walked22/Stacy/climate2/both.png

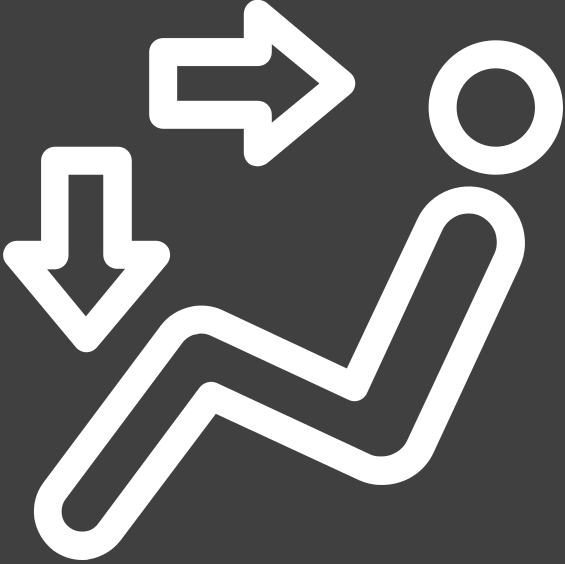
climate2/both.png
