walked22/Stacy/climate2/cold.png

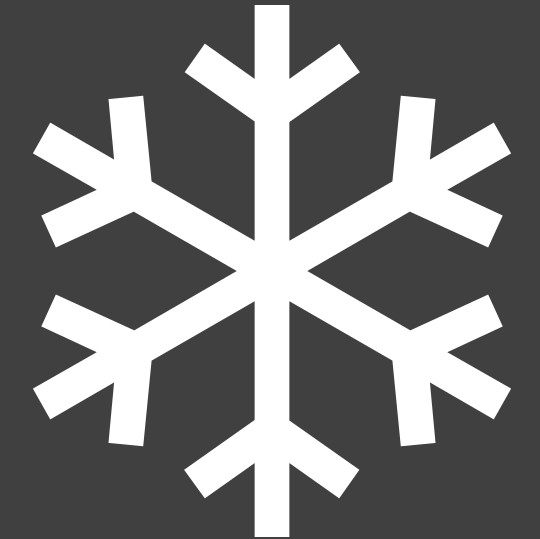
climate2/cold.png
