walked22/Stacy/climate2/defrost.png

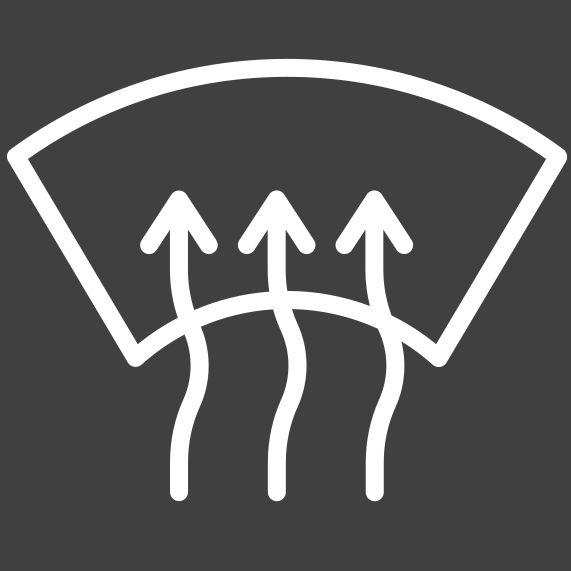
climate2/defrost.png
