walked22/Stacy/climate2/face.png

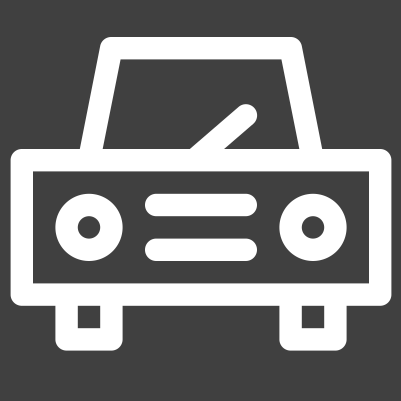
climate2/face.png
