walked22/Stacy/climate2/fan.png

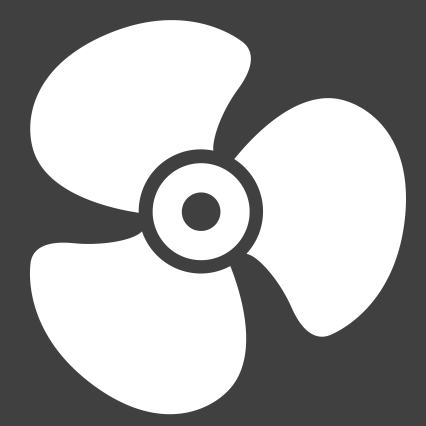
climate2/fan.png
