walked22/Stacy/climate2/feet.png

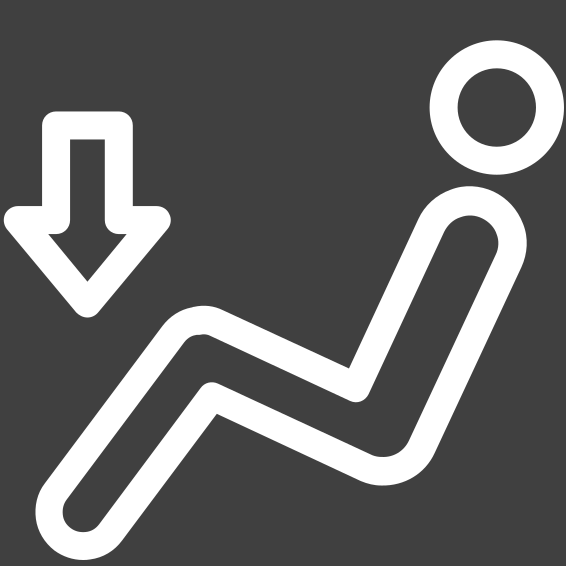
climate2/feet.png
