walked22/Stacy/climate2/frost-png-2.png

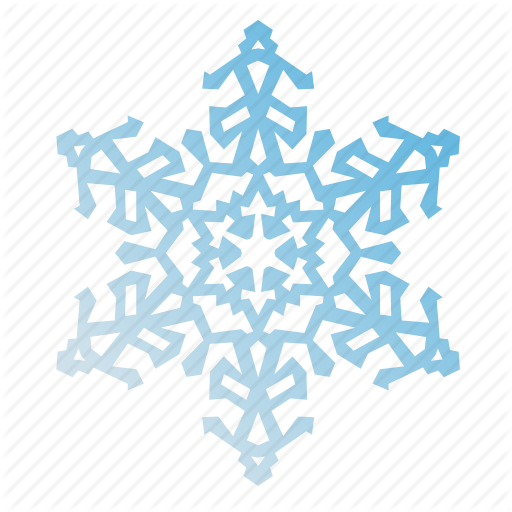
climate2/frost-png-2.png
