walked22/Stacy/climate2/hot.png

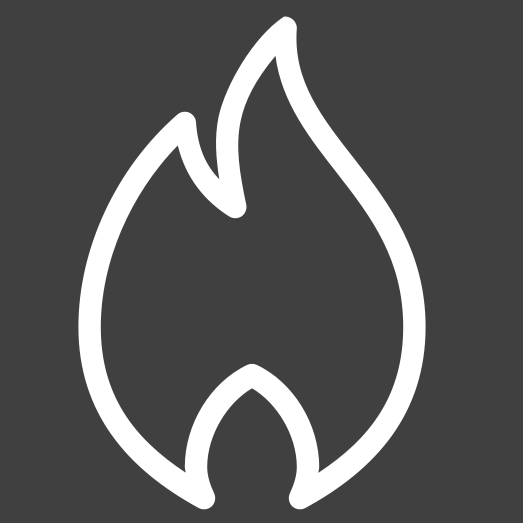
climate2/hot.png
