walked22/Stacy/climate2/inside.png

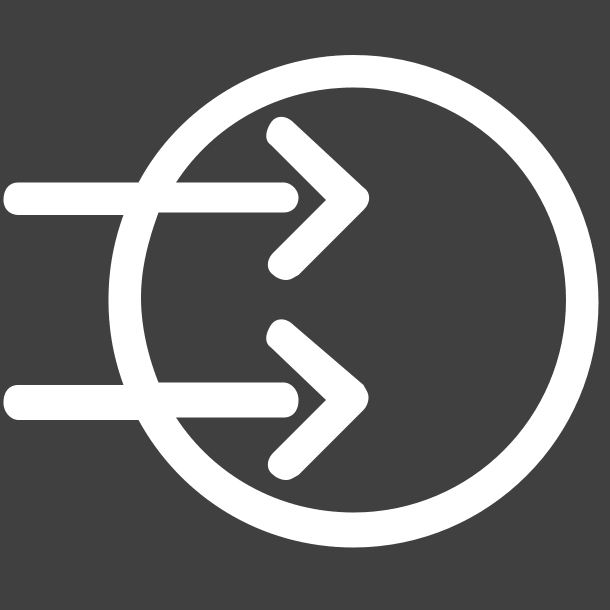
climate2/inside.png
