walked22/Stacy/climate2/light.png

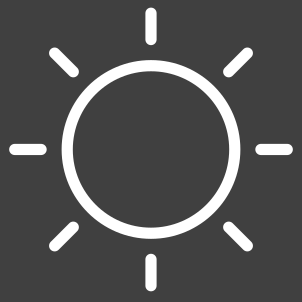
climate2/light.png
