walked22/Stacy/climate2/outside.png

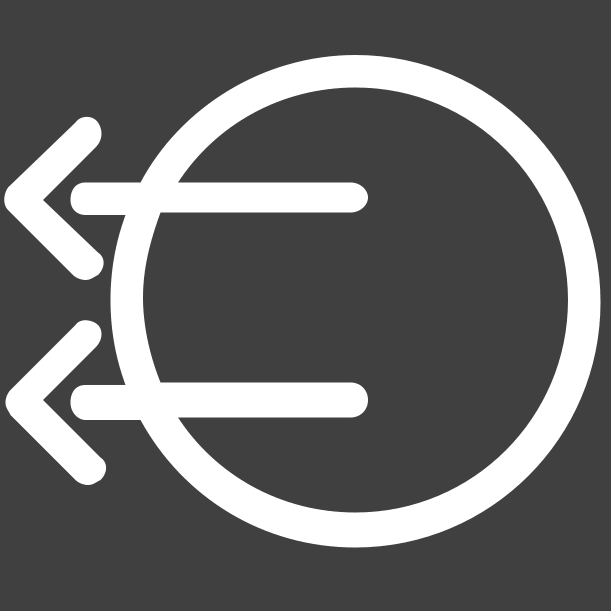
climate2/outside.png
