walked22/Stacy/climate2/outsideAir.png

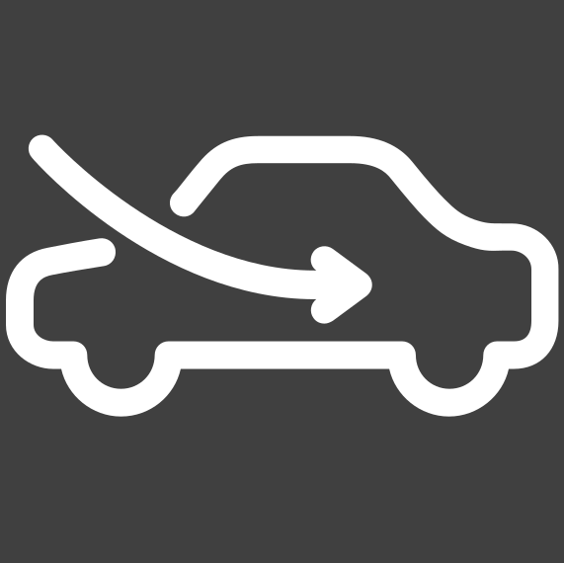
climate2/outsideAir.png
