walked22/Stacy/climate2/profile.png

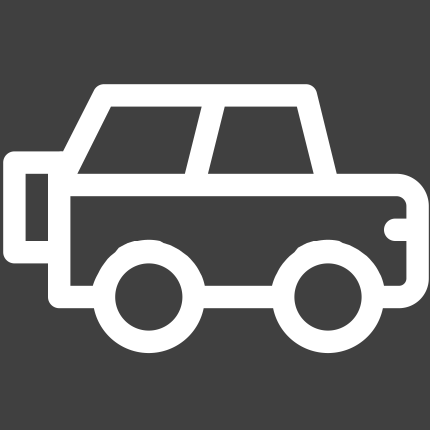
climate2/profile.png
