walked22/Stacy/Cluster/batt.png

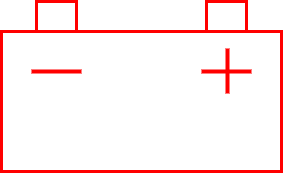
Cluster/batt.png
