walked22/Stacy/Cluster/Geo.png

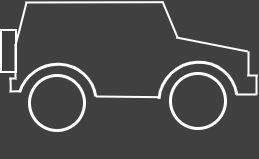
Cluster/Geo.png
