walked22/Stacy/Cluster/GeoBack.png

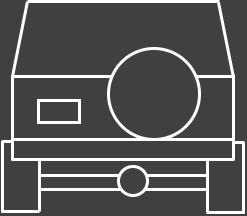
Cluster/GeoBack.png
