walked22/Stacy/Cluster/highs.png

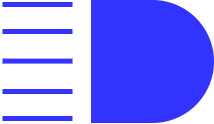
Cluster/highs.png
