walked22/Stacy/Cluster/left.png

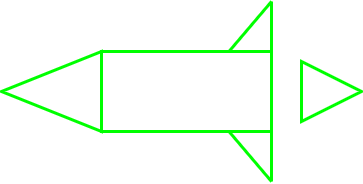
Cluster/left.png
