walked22/Stacy/Cluster/right.png

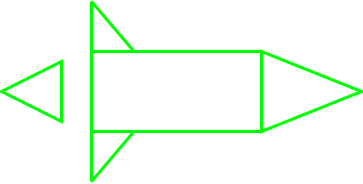
Cluster/right.png
